jbilander/JTAG-Connect/images/PCB_panel_v-scoring.jpg

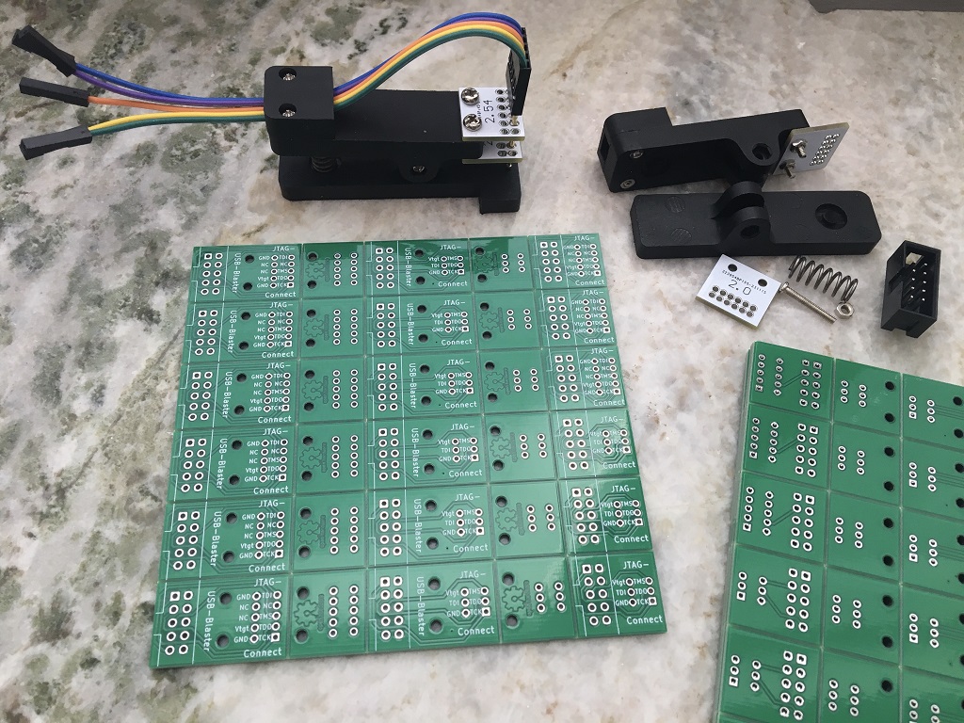
images/PCB_panel_v-scoring.jpg
